lismarc/compaq-portable-plasma-to-hdmi/photos/cp3_3.png

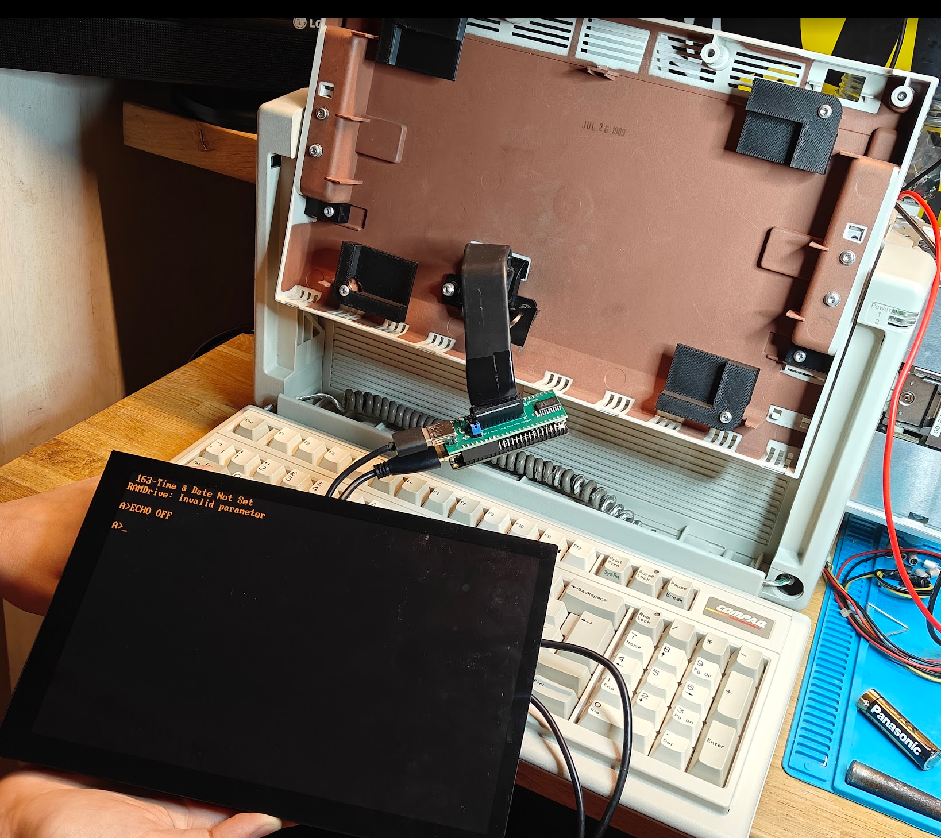
photos/cp3_3.png
